pe1mew/windmeters-modbus-interface/images/IMG_20260714_122643.jpg

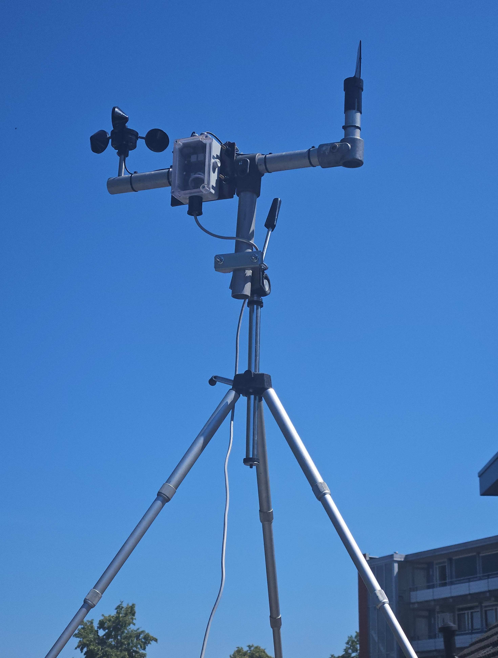
images/IMG_20260714_122643.jpg
