pe1mew/windmeters-modbus-interface/images/IMG_20260714_210950.jpg

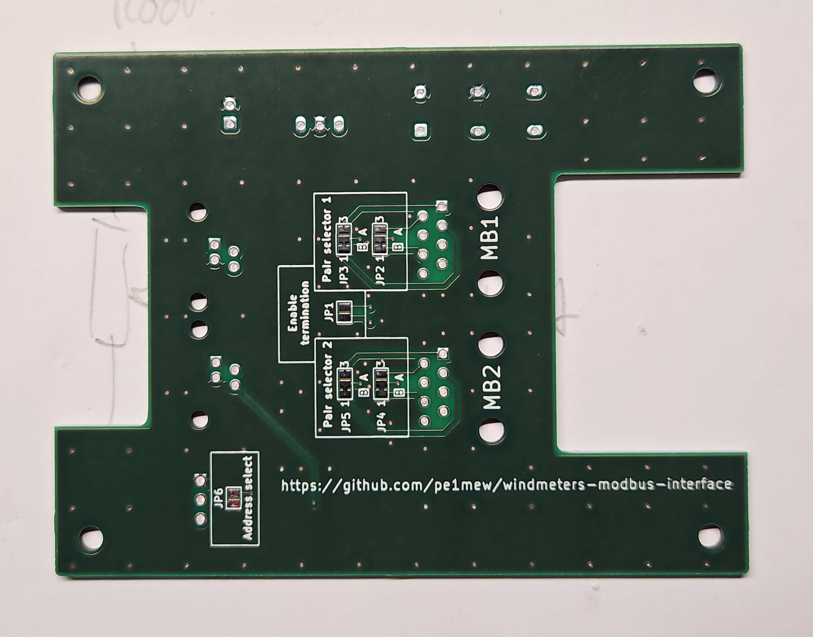
images/IMG_20260714_210950.jpg
